JohnCrash/kossel20x20/endstop_new.scad

include <vertex.scad>
width = 12.8;
height = 6;
length = 5.8;
 
module endstop(h,offset=2,outer=1)
{
	difference()
	{
		translate([-7,-15,-h/2])cube([19+length+outer+offset,30,h]);
		extrusion_cutout(2*h,2*extra_radius);
		cube([16,6,h],center=true);
		for(a=[1,-1])
		{
			translate([0,-6*a,0])
				rotate([90*a,0,0])
					cylinder(r=m3_radius,h=10);
			translate([0,-5*a,0])
			rotate([90*a,0,0])
			cylinder(r1=8,r2=m3_radius,h=5);
		}
		translate([13+offset,0,0])cube([length+2*extra_radius,width+2*extra_radius,h],center=true);
		translate([2+offset,-width/2,h/2-2])cube([10,width,5]);
	}
}

endstop(h=10,outer=2,offset=5);
