JohnCrash/kossel20x20/test.scad

difference()
{
	cube([50,50,10]);
	translate([5,5,0])cube([40,20,10]);
}
